jordiorlando/bcan/electronics/beacon/v1.1/images/beacon-brd.png

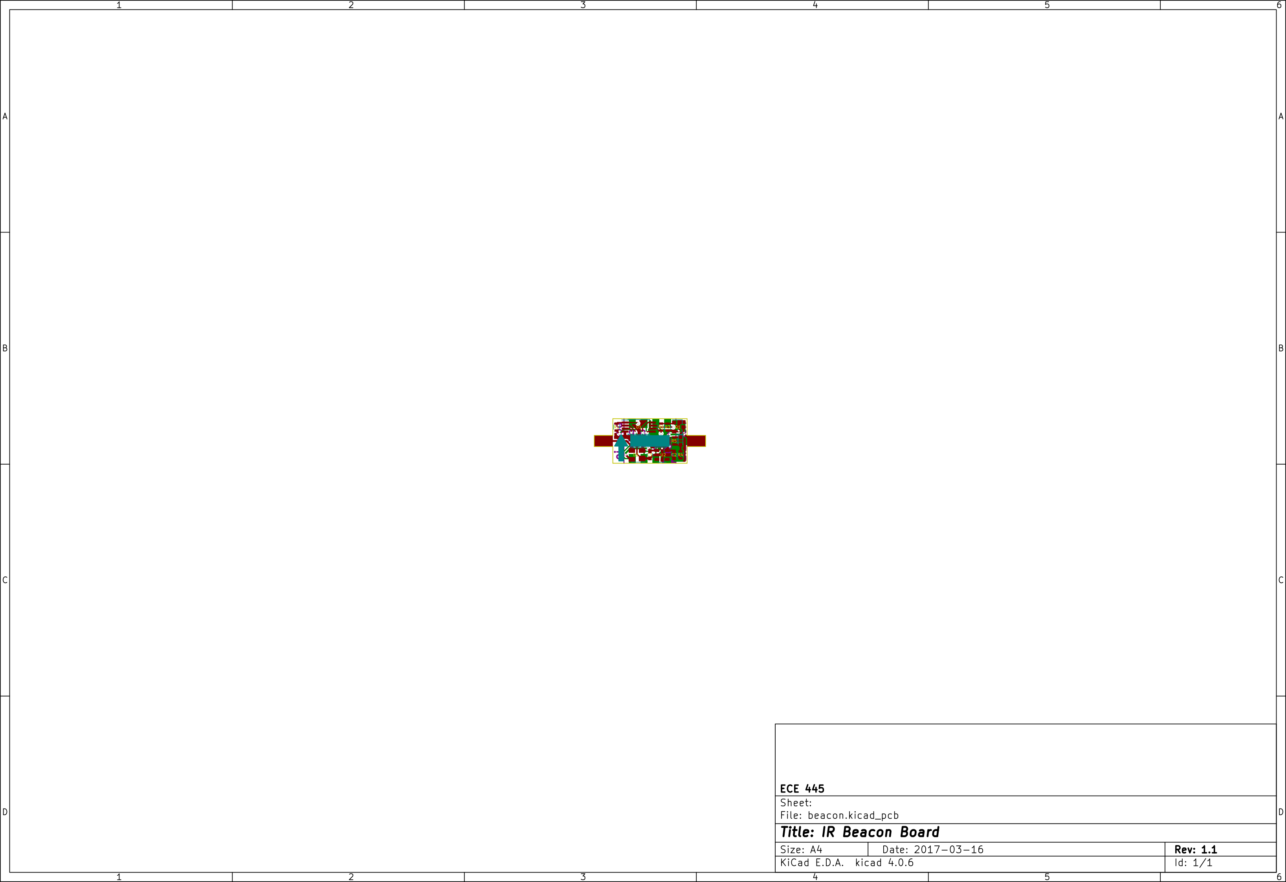
electronics/beacon/v1.1/images/beacon-brd.png
