jordiorlando/bcan/electronics/beacon/v1.1/images/beacon_3d_front.png

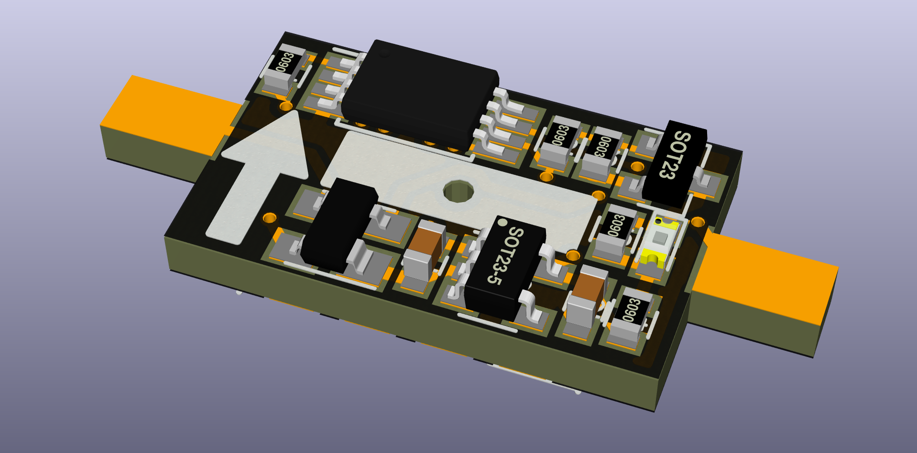
electronics/beacon/v1.1/images/beacon_3d_front.png
