jordiorlando/bcan/electronics/locomotive/images/locomotive-B.Cu.png

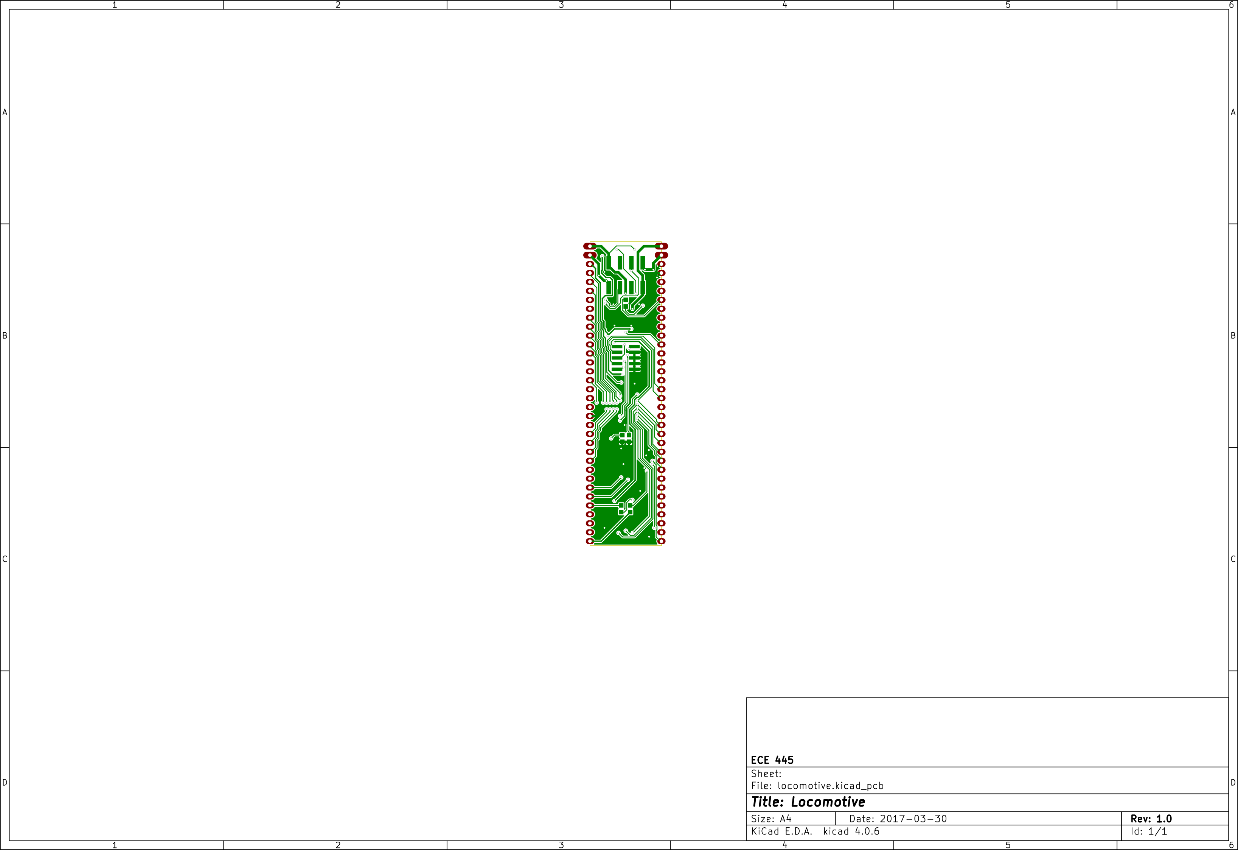
electronics/locomotive/images/locomotive-B.Cu.png
