jordiorlando/bcan/electronics/locomotive/images/locomotive_3d_back.png

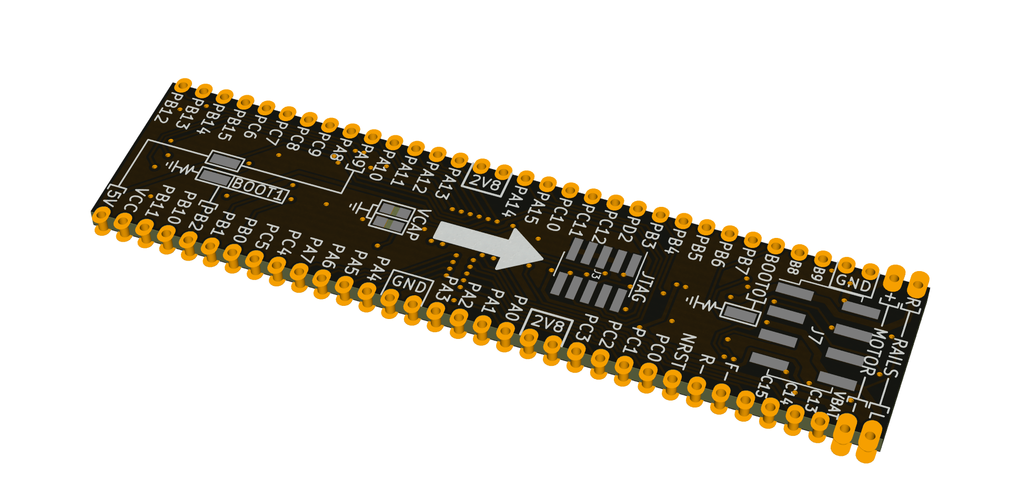
electronics/locomotive/images/locomotive_3d_back.png
