jordiorlando/bcan/electronics/locomotive/images/locomotive_3d_bottom.png

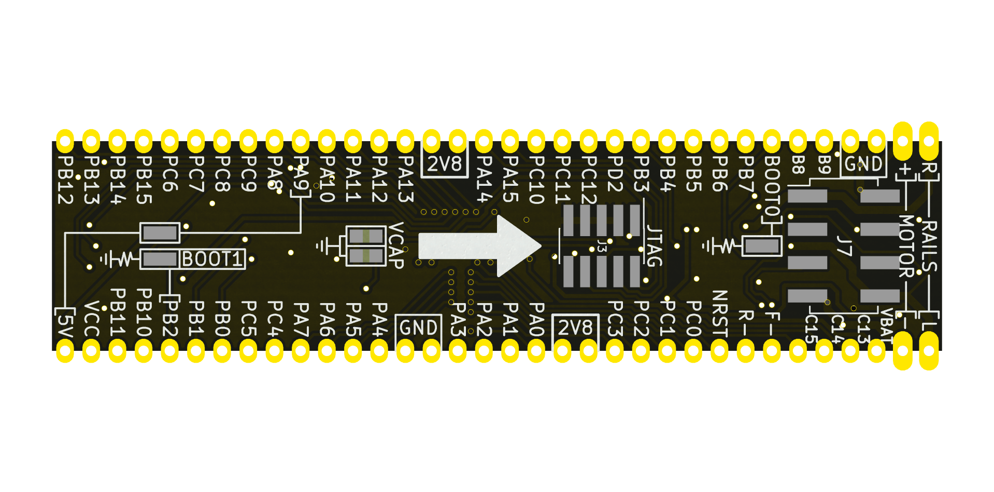
electronics/locomotive/images/locomotive_3d_bottom.png
