jordiorlando/bcan/electronics/locomotive/images/locomotive_3d_side.png

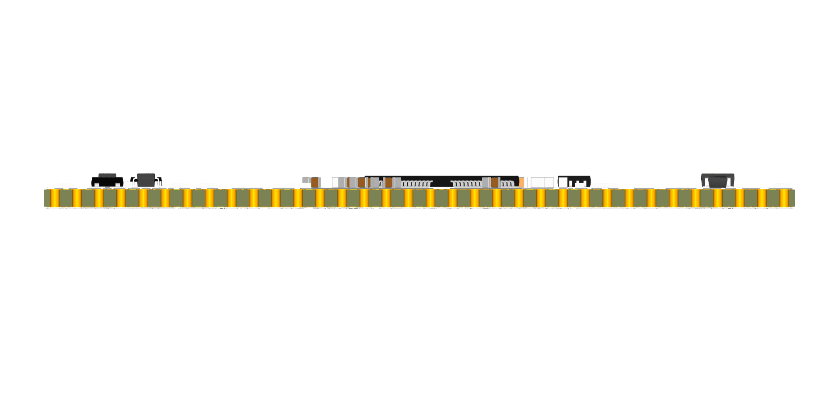
electronics/locomotive/images/locomotive_3d_side.png
