jordiorlando/bcan/electronics/locomotive/images/locomotive_3d_top.png

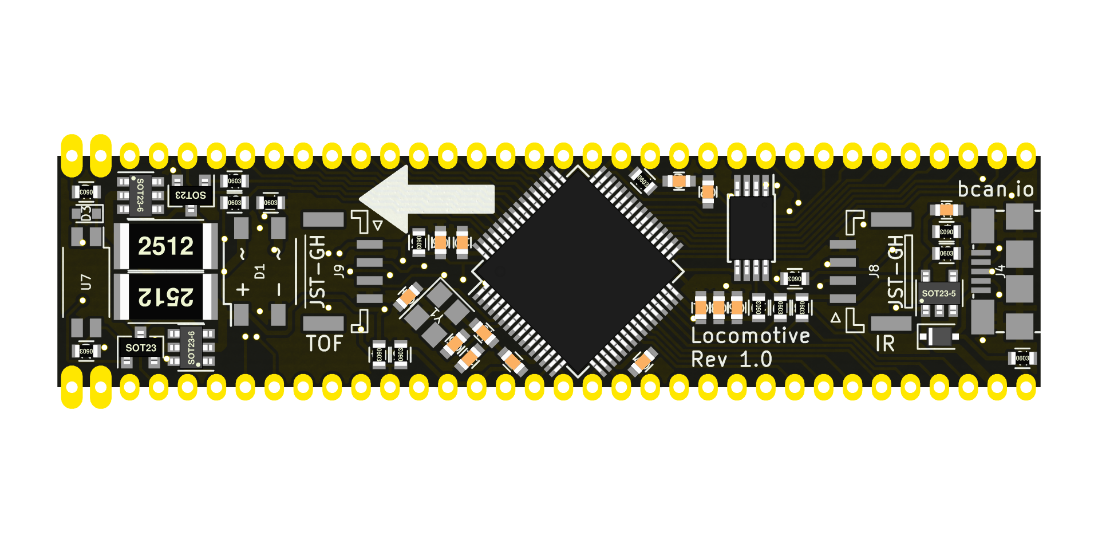
electronics/locomotive/images/locomotive_3d_top.png
