jordiorlando/bcan/mechanical/Atlas_HO_Code83.png

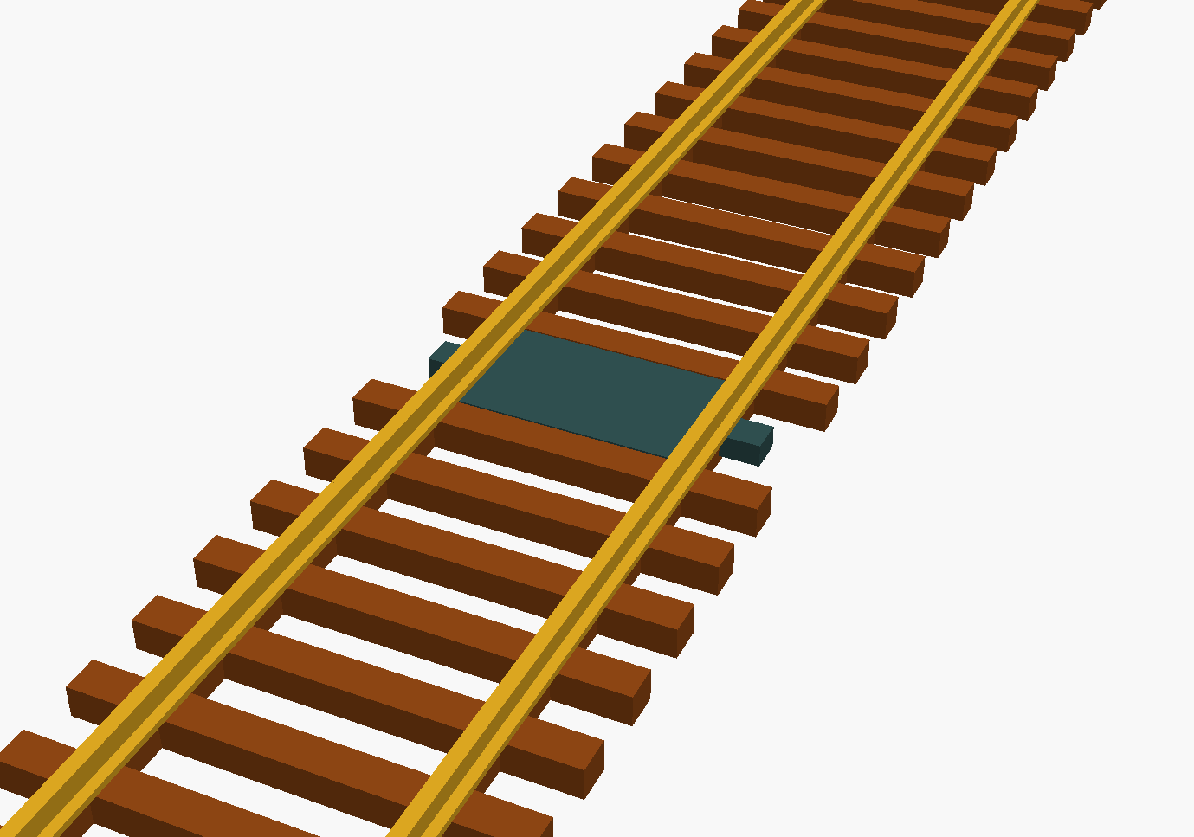
mechanical/Atlas_HO_Code83.png
